christopherdean11/battery-led-strip/BatteryLedStripDriver-R0/Outputs/PCB-3D-raytraced.png

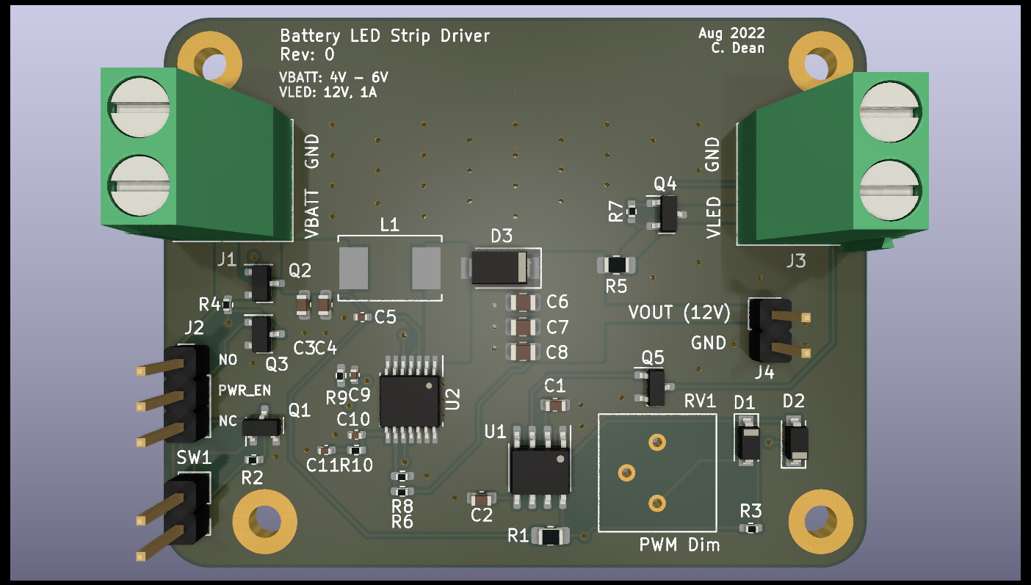
BatteryLedStripDriver-R0/Outputs/PCB-3D-raytraced.png
