christopherdean11/battery-led-strip/BatteryLedStripDriver-R0/Outputs/PCB-3D.png

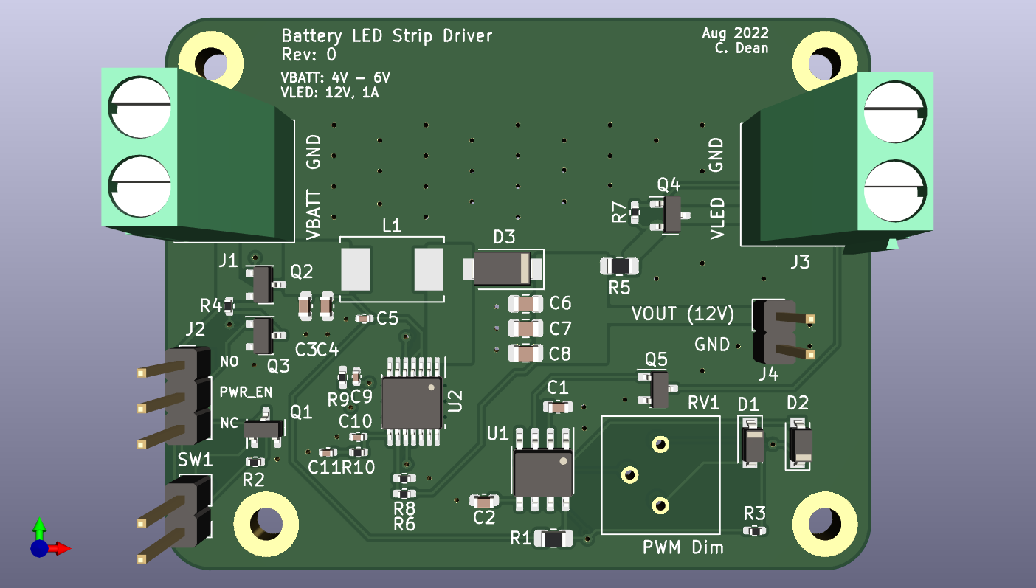
BatteryLedStripDriver-R0/Outputs/PCB-3D.png
